pollen-robotics/reachy-mini-skins/Christmas_Tree_Skin/Christmas Tree Skin - Tree_top_front.stl

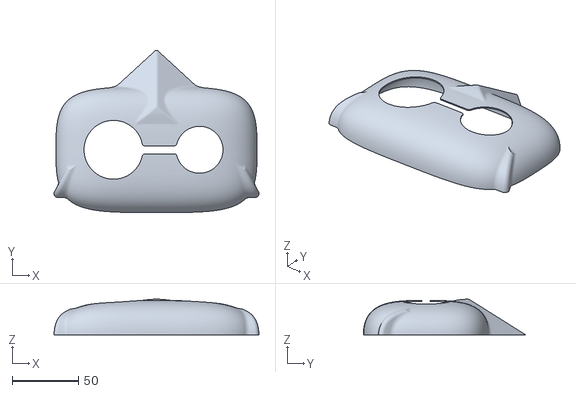
[picture p32: CAD file, 2026-03-24]
Christmas_Tree_Skin/Christmas Tree Skin - Tree_top_front.stl
154.9 x 122.6 x 27.0
