pollen-robotics/reachy-mini-skins/HuggingFace/step/hands/thumb1.step

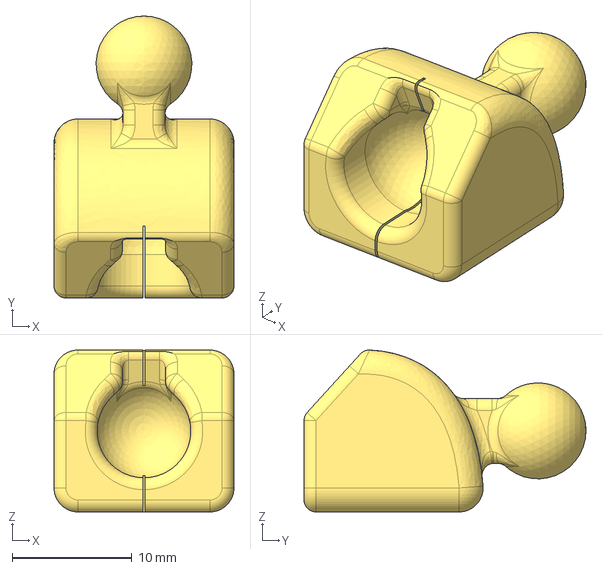
[picture p33: CAD file, 2026-03-25]
HuggingFace/step/hands/thumb1.step
15.0 x 23.5 x 13.5 mm
