pollen-robotics/reachy-mini-skins/HuggingFace/step/RM_HF - Back Skin.step

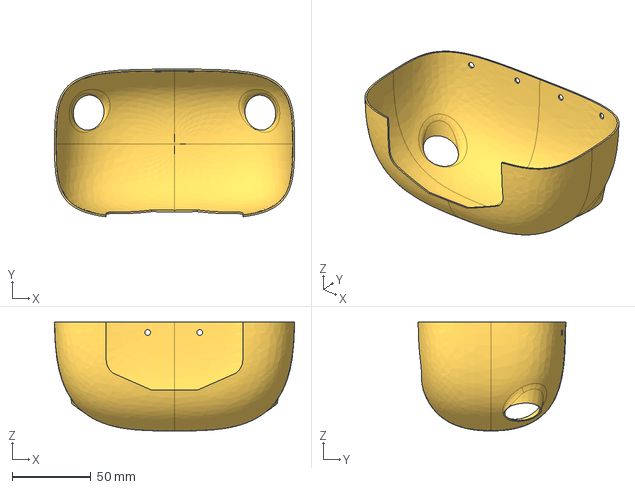
[picture p34: CAD file, 2026-03-25]
HuggingFace/step/RM_HF - Back Skin.step
152.0 x 93.6 x 69.0 mm
