pollen-robotics/reachy-mini-skins/pumpkin/Pumpkin_back.stl

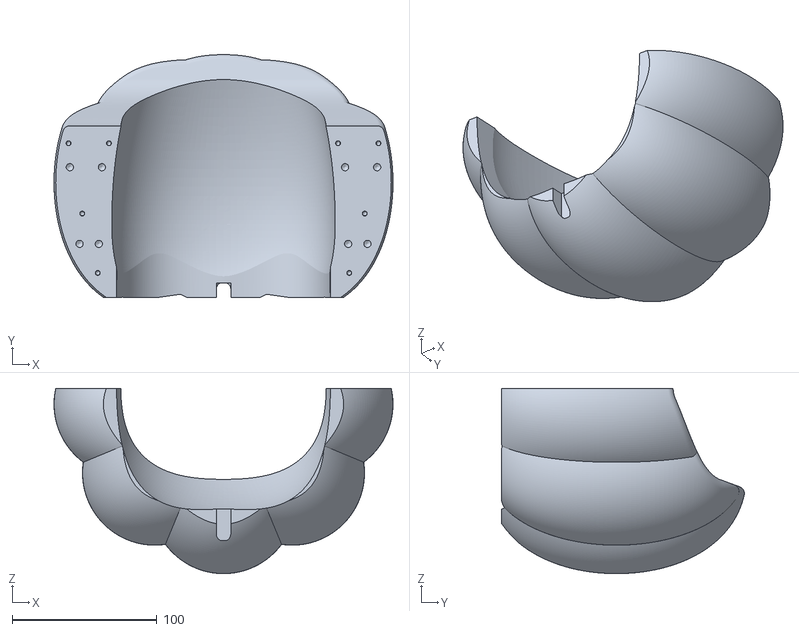
[picture p35: CAD file, 2026-03-26]
pumpkin/Pumpkin_back.stl
234.5 x 168.0 x 128.2
