pollen-robotics/reachy-mini-skins/Christmas_Tree_Skin/Christmas Tree Skin - Tree_base_back.stl

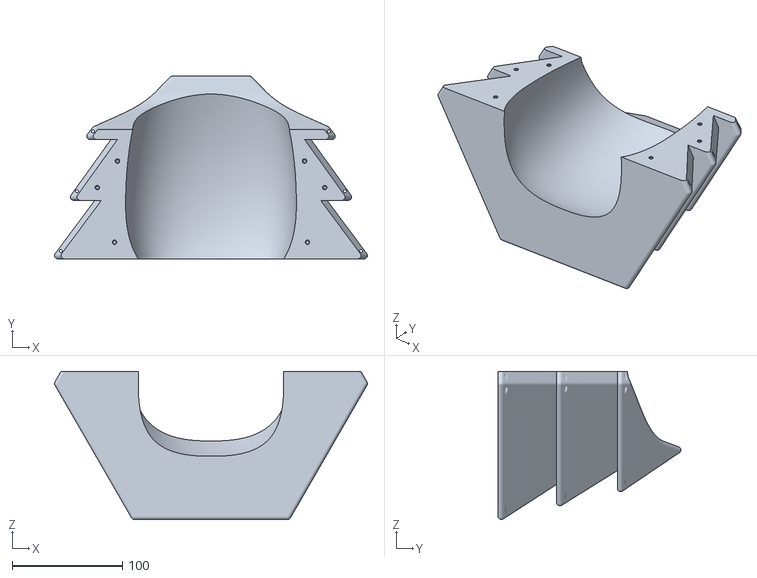
[picture p36: CAD file, 2026-03-24]
Christmas_Tree_Skin/Christmas Tree Skin - Tree_base_back.stl
283.3 x 165.5 x 134.0
