pollen-robotics/reachy-mini-skins/HuggingFace/step/hands/r_hand.step

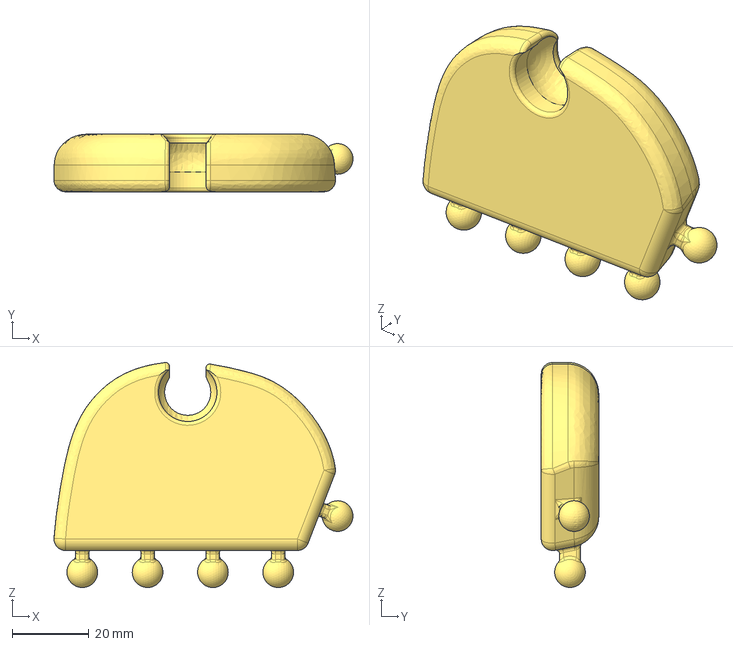
[picture p37: CAD file, 2026-03-25]
HuggingFace/step/hands/r_hand.step
77.8 x 15.0 x 58.6 mm
