pollen-robotics/reachy-mini-skins/HuggingFace/step/RM_HF - smalleye.step

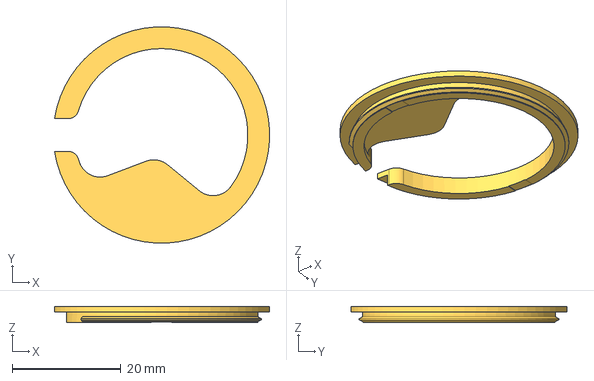
[picture p38: CAD file, 2026-03-25]
HuggingFace/step/RM_HF - smalleye.step
39.5 x 39.7 x 3.00 mm
