pollen-robotics/reachy-mini-skins/Christmas_Tree_Skin/Christmas Tree Skin - Tree_base_front.stl

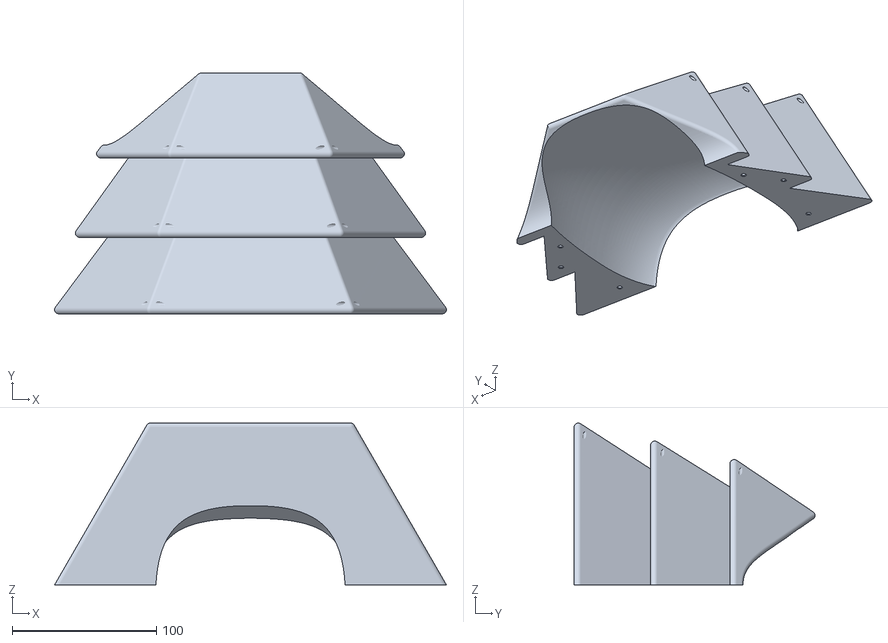
[picture p39: CAD file, 2026-03-24]
Christmas_Tree_Skin/Christmas Tree Skin - Tree_base_front.stl
271.6 x 166.9 x 112.1
