pollen-robotics/reachy-mini-skins/HuggingFace/step/RM_HF - clip.step

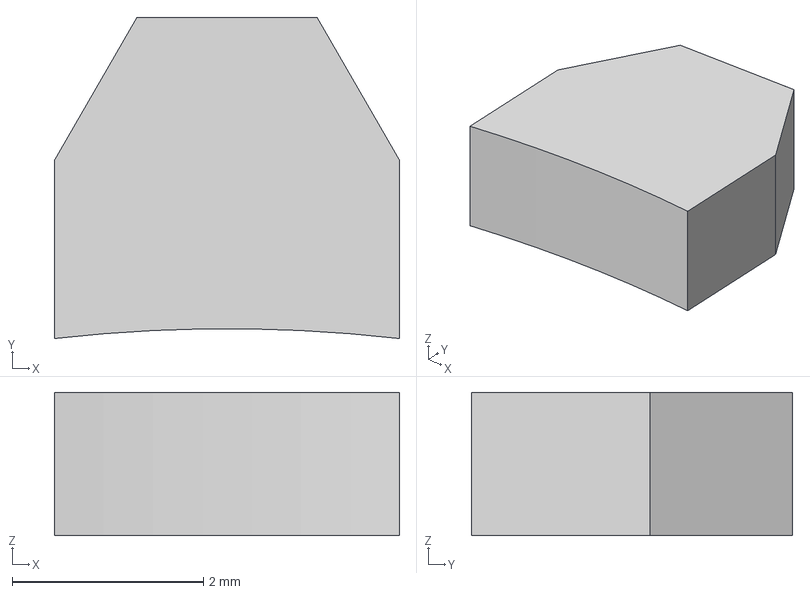
[picture p40: CAD file, 2026-03-25]
HuggingFace/step/RM_HF - clip.step
3.61 x 3.36 x 1.50 mm
