pollen-robotics/reachy-mini-skins/HuggingFace/step/RM_HF - bigeye.step

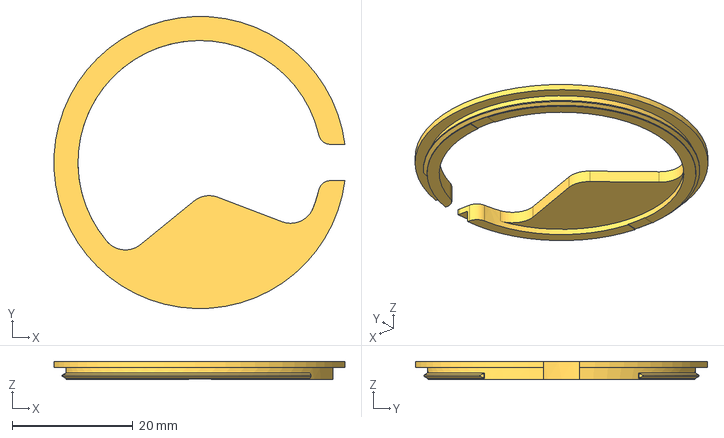
[picture p41: CAD file, 2026-03-25]
HuggingFace/step/RM_HF - bigeye.step
48.2 x 48.4 x 3.00 mm
