pollen-robotics/reachy-mini-skins/HuggingFace/step/hands/middle3.step

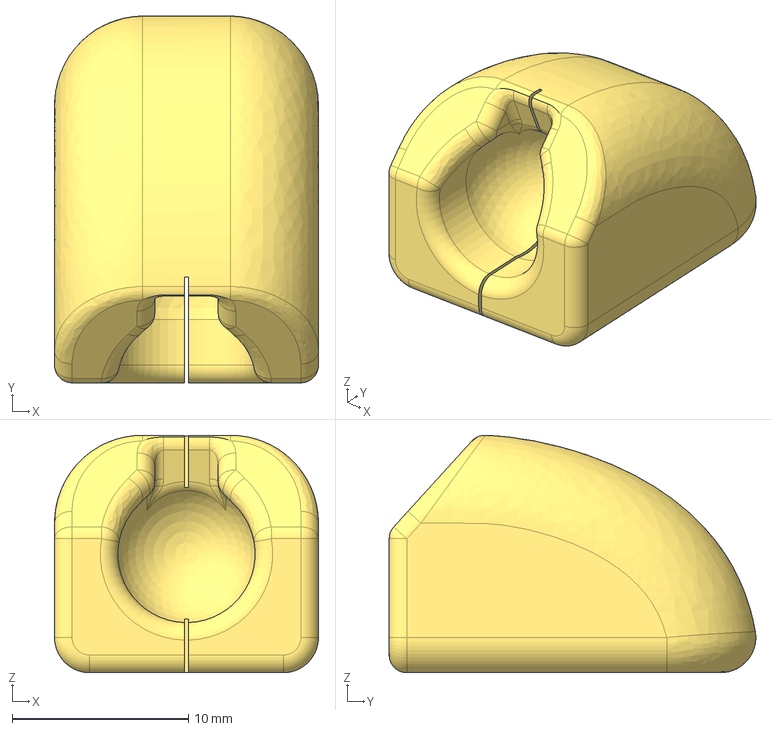
[picture p42: CAD file, 2026-03-25]
HuggingFace/step/hands/middle3.step
15.0 x 20.8 x 13.5 mm
