pollen-robotics/reachy-mini-skins/HuggingFace/step/RM_HF_skin_all_in_one.step

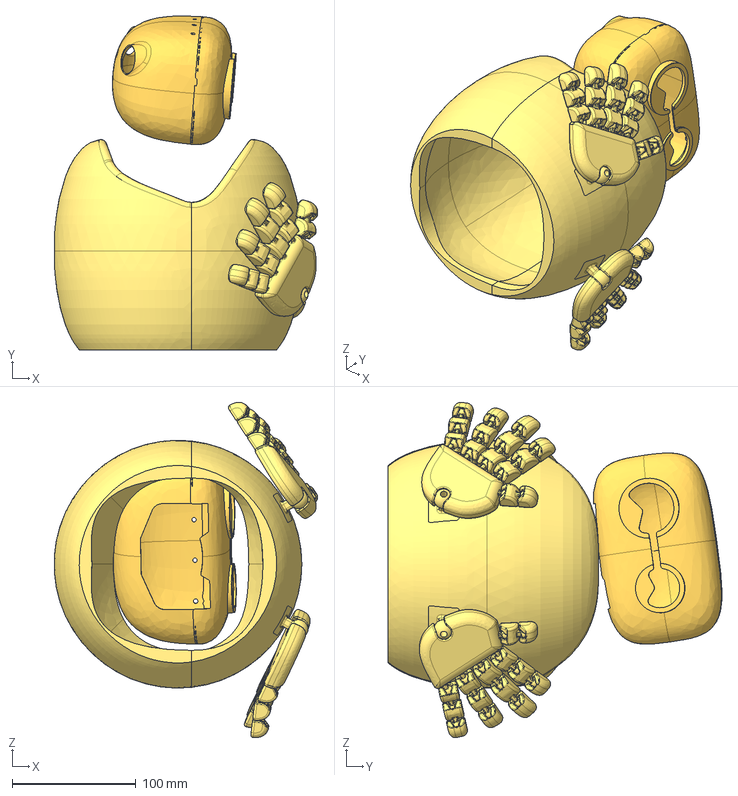
[picture p43: CAD file, 2026-03-25]
HuggingFace/step/RM_HF_skin_all_in_one.step
212.6 x 269.5 x 270.6 mm
fix_block_r
fix_block_l
bigeye
hf_front
front_skin2
clip
Back Skin
smalleye
test_phalanx x 10
test_phalanx_middle x 18
test_hand_r
test_hand_l
hf_back
