pollen-robotics/reachy-mini-skins/HuggingFace/step/hands/thumb2.step

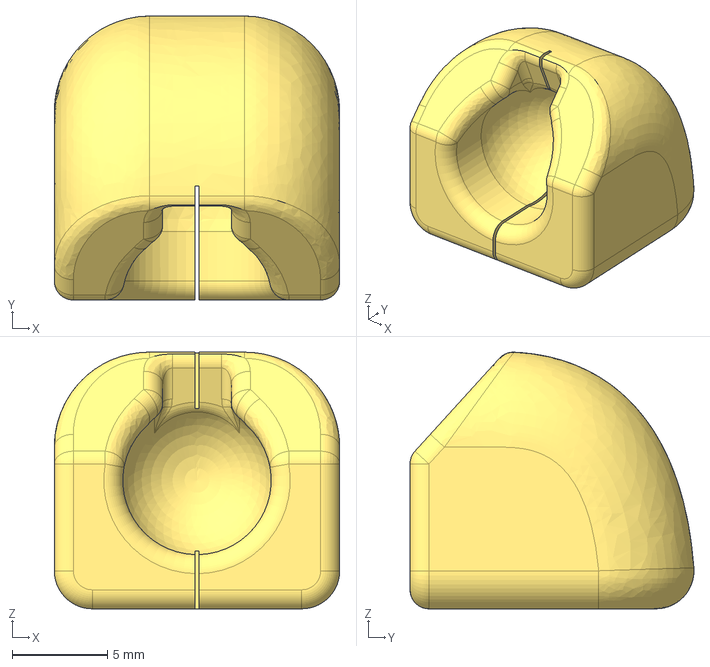
[picture p44: CAD file, 2026-03-25]
HuggingFace/step/hands/thumb2.step
15.0 x 14.9 x 13.5 mm
