pollen-robotics/reachy-mini-skins/HuggingFace/step/RM_HF - fix_block_l.step

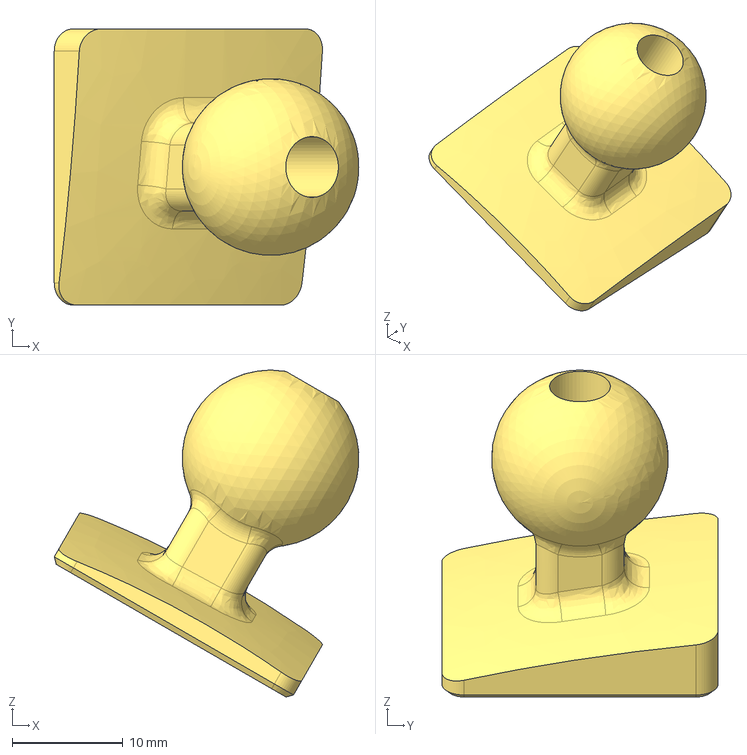
[picture p45: CAD file, 2026-03-25]
HuggingFace/step/RM_HF - fix_block_l.step
27.6 x 25.0 x 29.6 mm
